JeffTheSoldier/Hebrew-Letter-Clock/images/IMG_1932.jpg

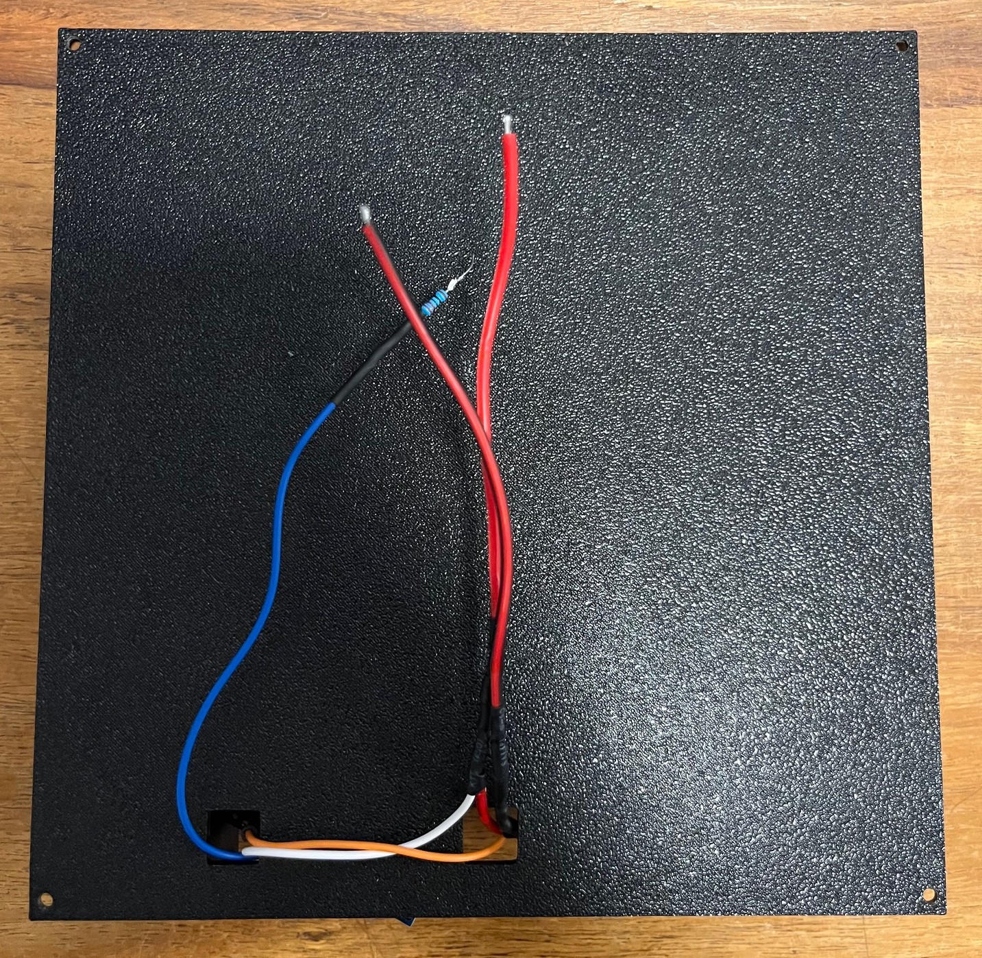
images/IMG_1932.jpg
