JeffTheSoldier/Hebrew-Letter-Clock/images/IMG_1934.jpg

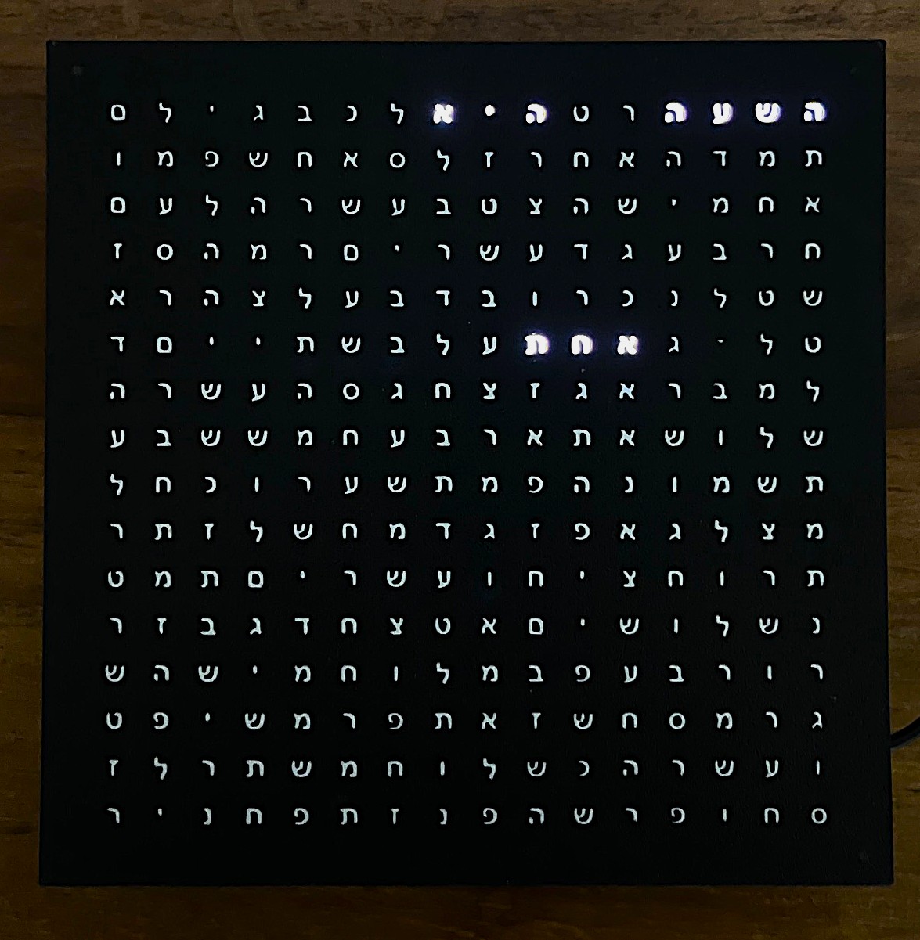
images/IMG_1934.jpg
