JeffTheSoldier/Hebrew-Letter-Clock/images/IMG_1935.jpg

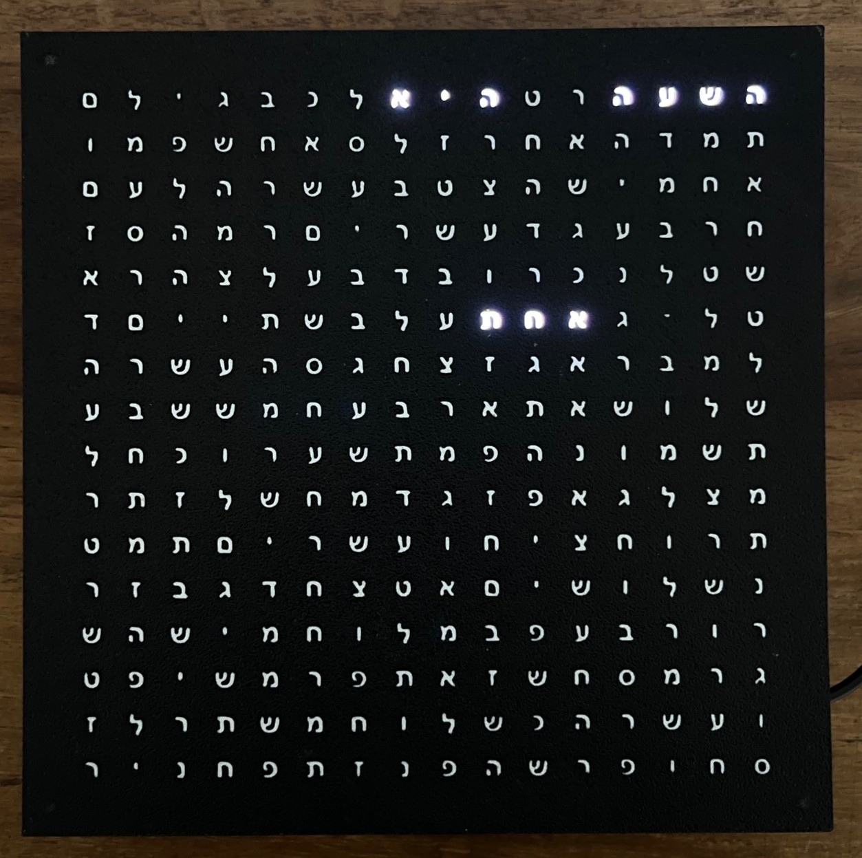
images/IMG_1935.jpg
